doesntfazer/frigate/Frigate V2 Final/Frigate.png

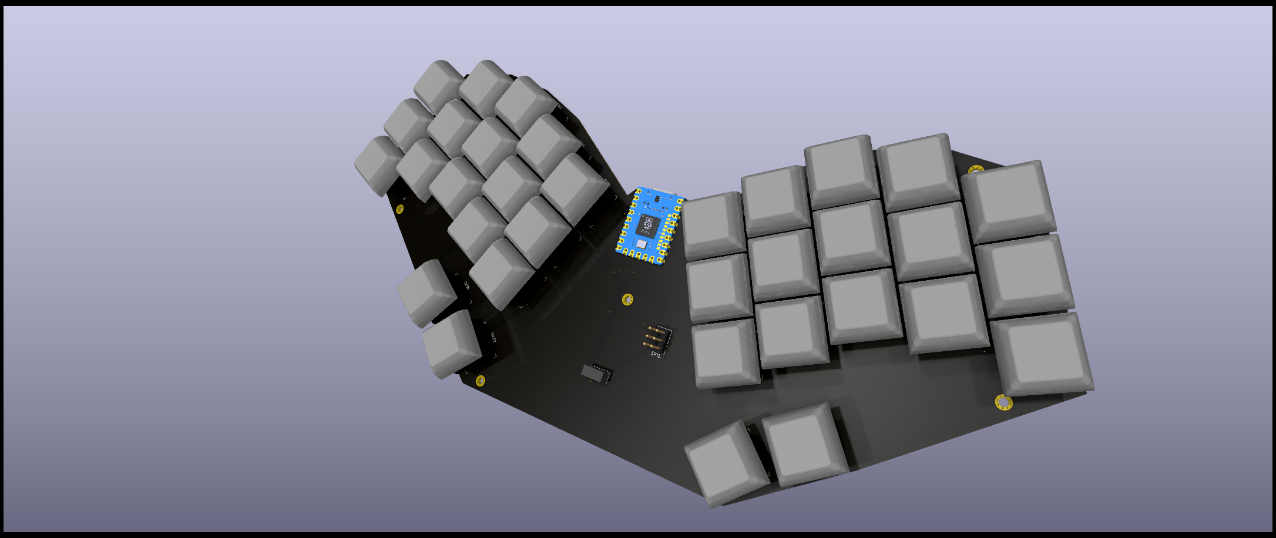
Frigate V2 Final/Frigate.png
