doesntfazer/frigate/Frigate V2 Final/DXF/Frigate-Edge_Cuts.dxf

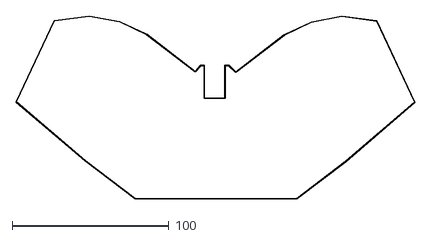
[picture p26: CAD file, 2023-05-12]
Frigate V2 Final/DXF/Frigate-Edge_Cuts.dxf
254.1 x 116.7
