doesntfazer/frigate/Frigate V2 Final/Case STL/Cirque-trackpad-pretty.stl

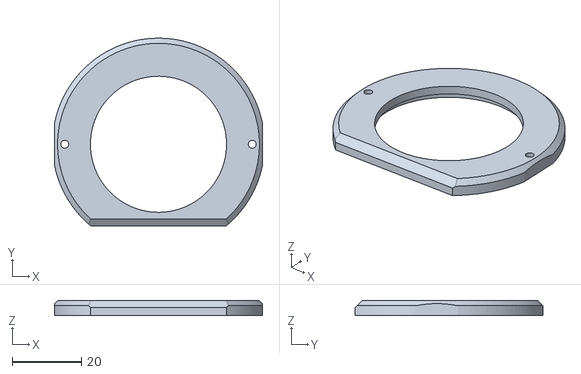
[picture p27: CAD file, 2023-05-12]
Frigate V2 Final/Case STL/Cirque-trackpad-pretty.stl
59.9 x 54.1 x 4.30
