doesntfazer/frigate/Frigate V2 Final/Case STL/cirquecover.stl

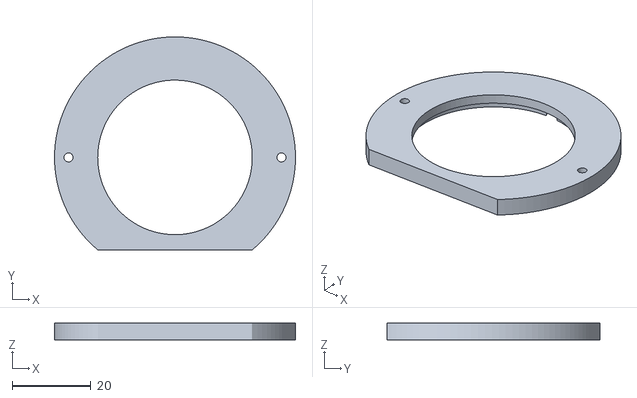
[picture p28: CAD file, 2023-05-12]
Frigate V2 Final/Case STL/cirquecover.stl
61.1 x 54.1 x 4.30
