doesntfazer/frigate/Frigate V2 Final/Case STL/plate.stl

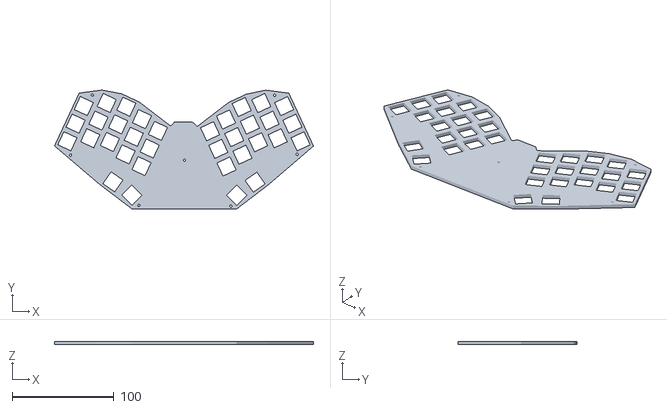
[picture p29: CAD file, 2023-05-12]
Frigate V2 Final/Case STL/plate.stl
254.0 x 116.6 x 3.00
