doesntfazer/frigate/Frigate V2 Final/Frigate/Frigate.kicad_sch

## KiCad design Frigate V2 Final/Frigate/Frigate.kicad_sch (2023-05-12)

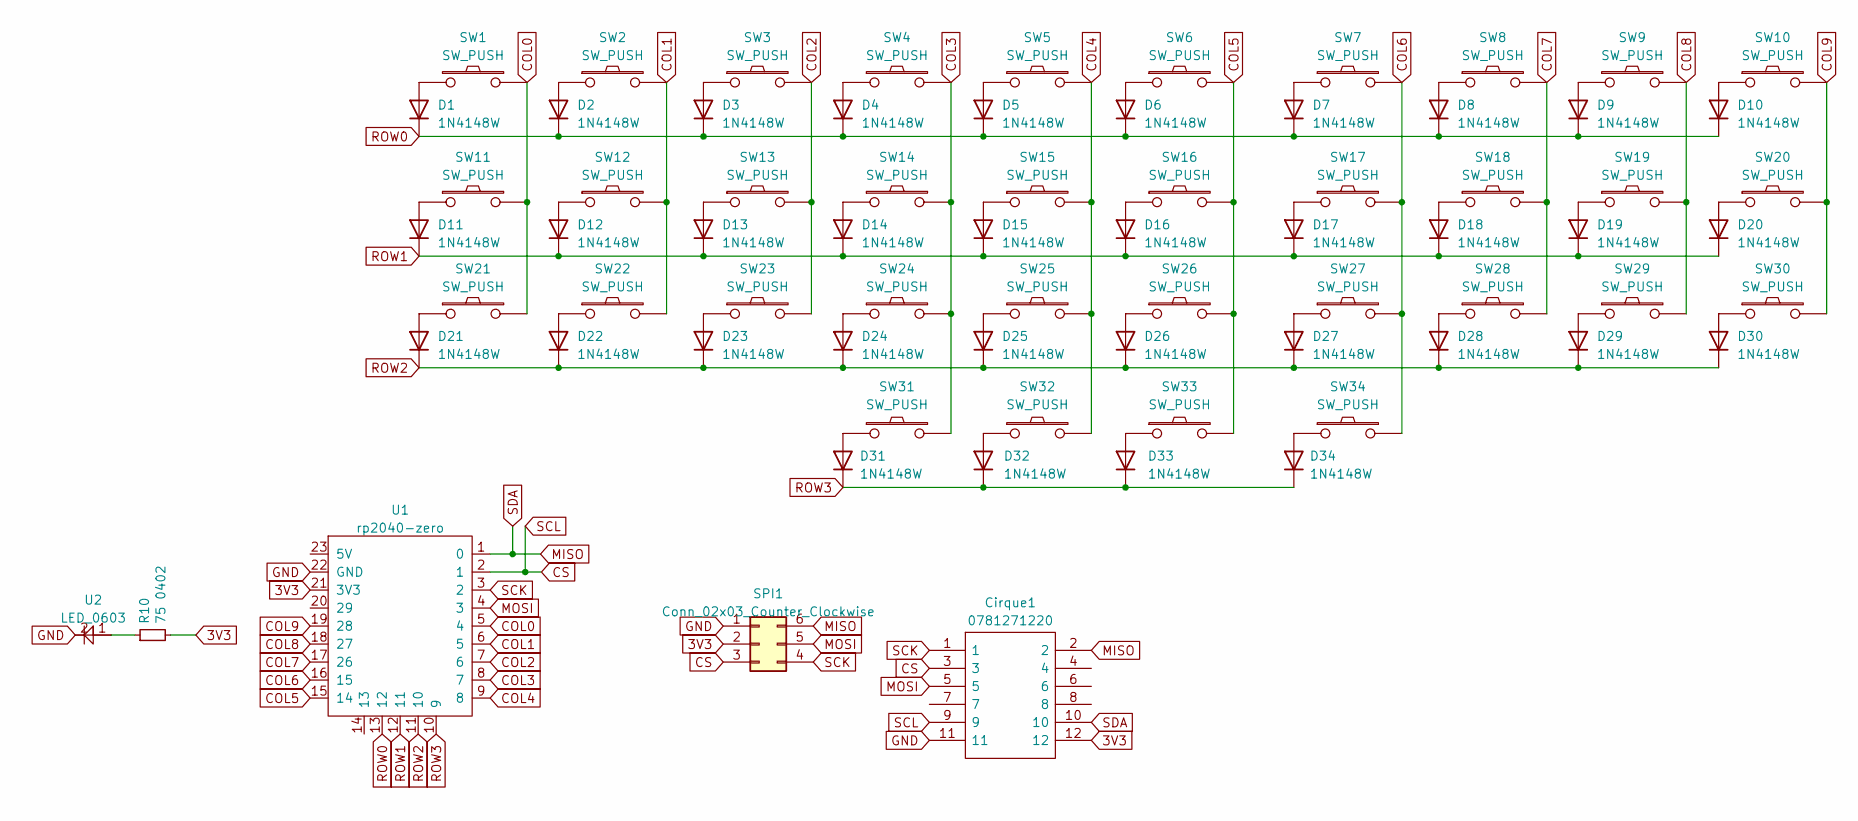
[picture p47: schematic Frigate.kicad_sch]

Parts:
Cirque1: 0781271220; Mouser Part Number 538-78127-1220
D1, D2, D3, D4, D5, D6, D7, D8, D9, D10, D11, D12, D13, D14, D15, D16, D17, D18, D19, D20, D21, D22, D23, D24, D25, D26, D27, D28, D29, D30, D31, D32, D33, D34: 1N4148W; D_SOD-123
R10: 75 0402; R_0402_1005Metric; JLC C25133
SPI1: Conn_02x03_Counter_Clockwise; PinHeader_2x03_P2.54mm_Vertical
SW1, SW2, SW3, SW4, SW5, SW6, SW7, SW8, SW9, SW10, SW11, SW12, SW13, SW14, SW15, SW16, SW17, SW18, SW19, SW20, SW21, SW22, SW23, SW24, SW25, SW26, SW27, SW28, SW29, SW30, SW31, SW32, SW33, SW34: SW_PUSH; Kailh_socket_MX_4fab
U1: rp2040-zero; rp2040-zero-tht-nocut
U2: LED_0603; JLC C2286

Connections:
3V3: Cirque1.12, R10.2, SPI1.2, U1.21 (3V3)
COL0: SW1.2, SW11.2, SW21.2, U1.5 (4)
COL1: SW2.2, SW12.2, SW22.2, U1.6 (5)
COL2: SW3.2, SW13.2, SW23.2, U1.7 (6)
COL3: SW4.2, SW14.2, SW24.2, SW31.2, U1.8 (7)
COL4: SW5.2, SW15.2, SW25.2, SW32.2, U1.9 (8)
COL5: SW6.2, SW16.2, SW26.2, SW33.2, U1.15 (14)
COL6: SW7.2, SW17.2, SW27.2, SW34.2, U1.16 (15)
COL7: SW8.2, SW18.2, SW28.2, U1.17 (26)
COL8: SW9.2, SW19.2, SW29.2, U1.18 (27)
COL9: SW10.2, SW20.2, SW30.2, U1.19 (28)
CS: Cirque1.3, Cirque1.9, SPI1.3, U1.2 (1)
GND: Cirque1.11, SPI1.1, U1.22 (GND), U2.2
MISO: Cirque1.2, Cirque1.10, SPI1.6, U1.1 (0)
MOSI: Cirque1.5, SPI1.5, U1.4 (3)
unnamed: D1.2 (A), SW1.1
unnamed: D2.2 (A), SW2.1
unnamed: D3.2 (A), SW3.1
unnamed: D4.2 (A), SW4.1
unnamed: D5.2 (A), SW5.1
unnamed: D6.2 (A), SW6.1
unnamed: D7.2 (A), SW7.1
unnamed: D8.2 (A), SW8.1
unnamed: D9.2 (A), SW9.1
unnamed: D10.2 (A), SW10.1
unnamed: D11.2 (A), SW11.1
unnamed: D12.2 (A), SW12.1
unnamed: D13.2 (A), SW13.1
unnamed: D14.2 (A), SW14.1
unnamed: D15.2 (A), SW15.1
unnamed: D16.2 (A), SW16.1
unnamed: D17.2 (A), SW17.1
unnamed: D18.2 (A), SW18.1
unnamed: D19.2 (A), SW19.1
unnamed: D20.2 (A), SW20.1
unnamed: D21.2 (A), SW21.1
unnamed: D22.2 (A), SW22.1
unnamed: D23.2 (A), SW23.1
unnamed: D24.2 (A), SW24.1
unnamed: D25.2 (A), SW25.1
unnamed: D26.2 (A), SW26.1
unnamed: D27.2 (A), SW27.1
unnamed: D28.2 (A), SW28.1
unnamed: D29.2 (A), SW29.1
unnamed: D30.2 (A), SW30.1
unnamed: D31.2 (A), SW31.1
unnamed: D32.2 (A), SW32.1
unnamed: D33.2 (A), SW33.1
unnamed: D34.2 (A), SW34.1
unnamed: R10.1, U2.1
ROW0: D1.1 (K), D2.1 (K), D3.1 (K), D4.1 (K), D5.1 (K), D6.1 (K), D7.1 (K), D8.1 (K), D9.1 (K), D10.1 (K), U1.13 (12)
ROW1: D11.1 (K), D12.1 (K), D13.1 (K), D14.1 (K), D15.1 (K), D16.1 (K), D17.1 (K), D18.1 (K), D19.1 (K), D20.1 (K), U1.12 (11)
ROW2: D21.1 (K), D22.1 (K), D23.1 (K), D24.1 (K), D25.1 (K), D26.1 (K), D27.1 (K), D28.1 (K), D29.1 (K), D30.1 (K), U1.11 (10)
ROW3: D31.1 (K), D32.1 (K), D33.1 (K), D34.1 (K), U1.10 (9)
SCK: Cirque1.1, SPI1.4, U1.3 (2)
